IHomes/remotegardensite/fritzing/fritzing_protoboard.png

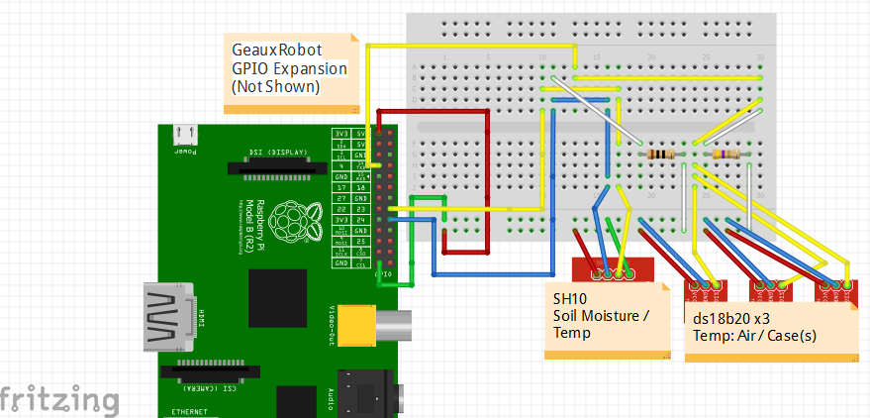
fritzing/fritzing_protoboard.png
