IHomes/remotegardensite/rf_modeling/splat/example_misc_summary_files/Base_xxdBGain_coverage_dBm.png

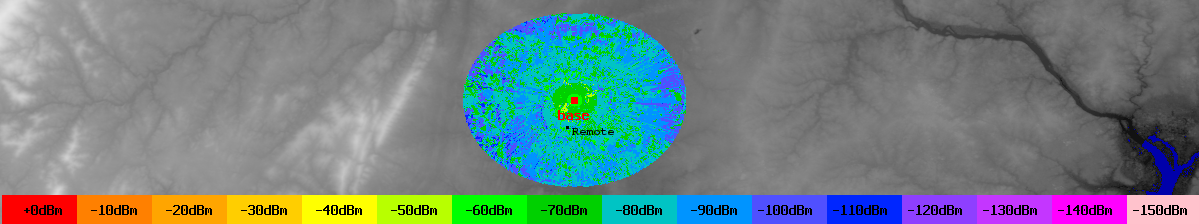
rf_modeling/splat/example_misc_summary_files/Base_xxdBGain_coverage_dBm.png
