IHomes/remotegardensite/rf_modeling/splat/example_misc_summary_files/Data_from_Base_to_remote.png

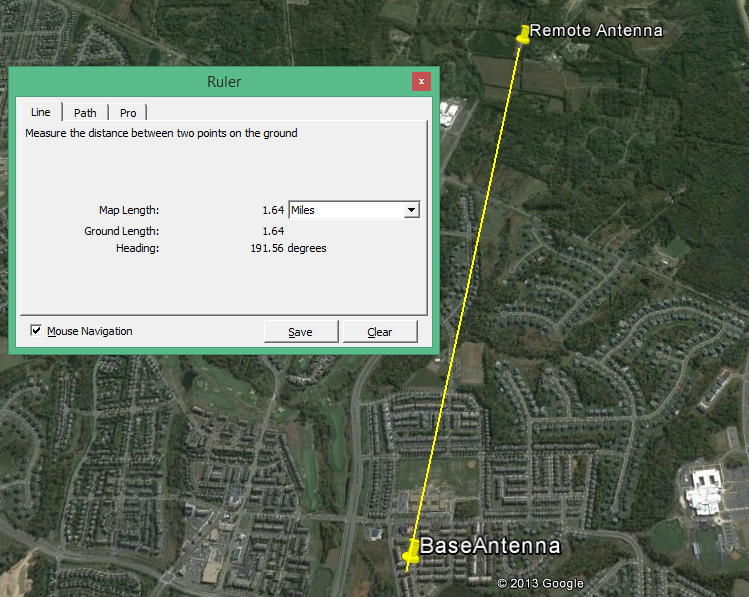
rf_modeling/splat/example_misc_summary_files/Data_from_Base_to_remote.png
