IHomes/remotegardensite/rf_modeling/splat/example_misc_summary_files/Data_from_Remote_to_Base.png

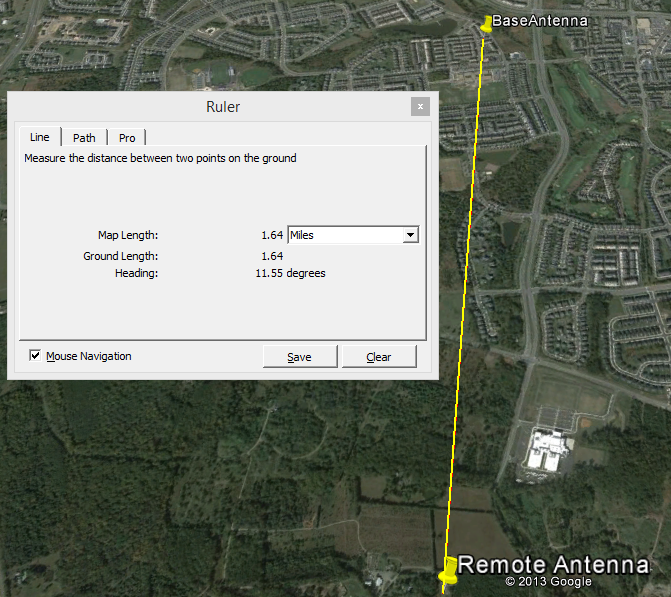
rf_modeling/splat/example_misc_summary_files/Data_from_Remote_to_Base.png
