IHomes/remotegardensite/rf_modeling/splat/example_misc_summary_files/Remote_to_Base_LineofSight.png

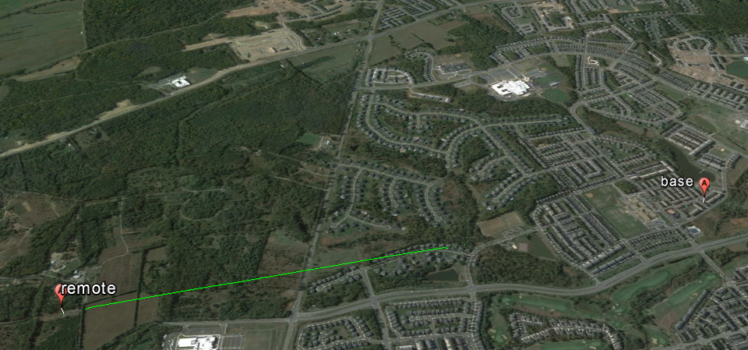
rf_modeling/splat/example_misc_summary_files/Remote_to_Base_LineofSight.png
