IHomes/remotegardensite/rf_modeling/splat/example_misc_summary_files/Remote_xxdBGain_coverage_fieldStrength.png

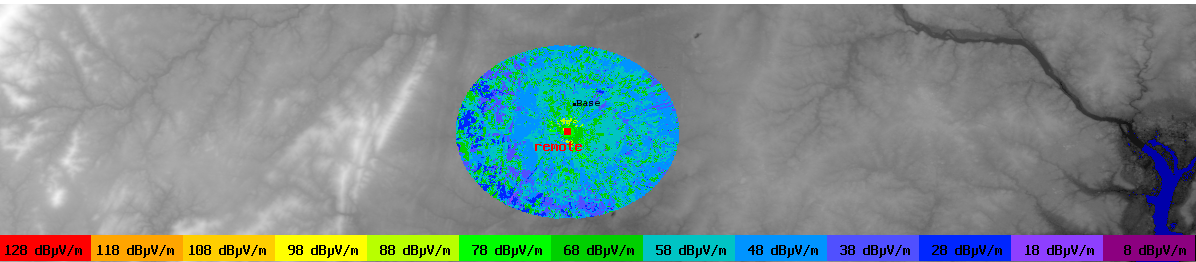
rf_modeling/splat/example_misc_summary_files/Remote_xxdBGain_coverage_fieldStrength.png
