IHomes/remotegardensite/rf_modeling/splat/example_output_base17dBi_to_remote10dBi/elavation.png

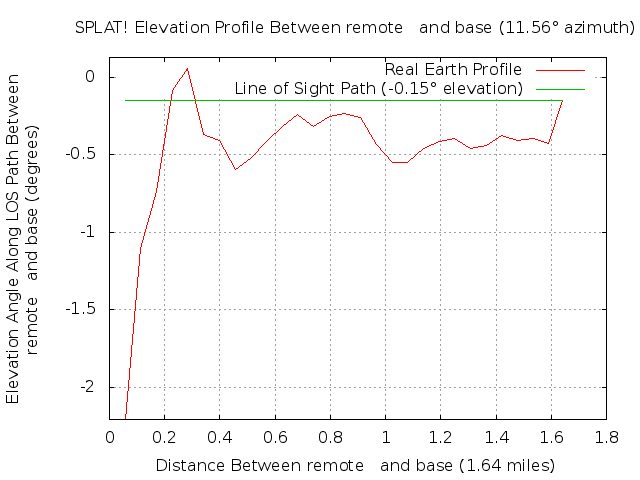
rf_modeling/splat/example_output_base17dBi_to_remote10dBi/elavation.png
