IHomes/remotegardensite/rf_modeling/splat/example_output_remote10dBi_to_base17dBi/loss.png

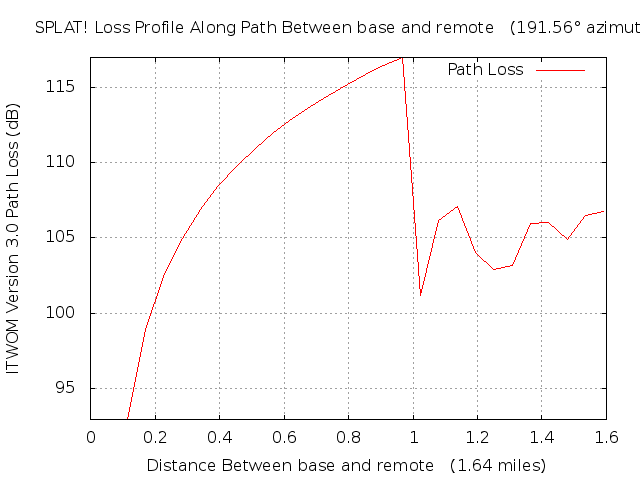
rf_modeling/splat/example_output_remote10dBi_to_base17dBi/loss.png
